ManCloud/RGB_PCBs/Multi-Out/Sony/Multi-Out_S_Bottom.png

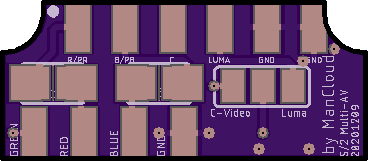
Multi-Out/Sony/Multi-Out_S_Bottom.png
