ManCloud/RGB_PCBs/VSAB/VSAB_75R_P/VSAB_75R_P_Top.png

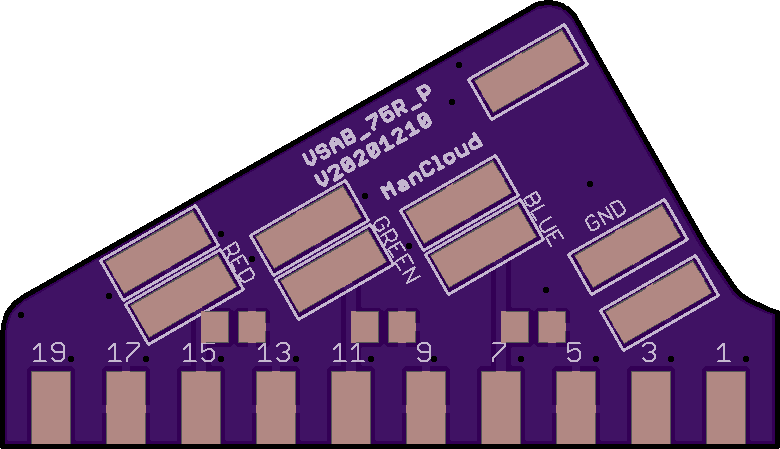
VSAB/VSAB_75R_P/VSAB_75R_P_Top.png
